hulakov/NosClock/esphome/components/nosclock/nos_controller.h

#pragma once
#include "esphome/core/component.h"
#include "esphome/components/i2c/i2c.h"
#include "esphome/components/time/real_time_clock.h"
#include "esphome/components/output/float_output.h"
#include "esphome/components/light/light_state.h"

#include "nos_effect.h"
#include "effect_solid.h"
#include "effect_digit_sync.h"
#include "effect_scanner.h"
#include "effect_scanner_dual.h"
#include "effect_scanner_split.h"
#include "aw9523.h"
#include "nos_tubes.h"

namespace nosclock {

// Calibrated hardware output limits (1% -> min, 100% -> max)
static constexpr float BACKLIGHT_MIN_RAW = 10.0f;
static constexpr float BACKLIGHT_MAX_RAW = 255.0f;

static constexpr float DOTS_R_MIN_RAW = 1.0f;
static constexpr float DOTS_R_MAX_RAW = 6.0f;

static constexpr float DOTS_G_MIN_RAW = 1.0f;
static constexpr float DOTS_G_MAX_RAW = 4.0f;

static constexpr float DOTS_B_MIN_RAW = 1.0f;
static constexpr float DOTS_B_MAX_RAW = 7.0f;

class NosController : public esphome::PollingComponent {
 public:
   NosController() : esphome::PollingComponent(20) {}

   void setup() override;
   void update() override;
   void dump_config() override;

   void set_i2c_bus(esphome::i2c::I2CBus *bus) { m_i2c_bus = bus; }
   void set_time(esphome::time::RealTimeClock *time) { m_time = time; }
   void set_tubes_light(esphome::light::LightState *light) { m_tubes_light = light; }
   void set_backlight_strip(esphome::light::LightState *strip) { m_backlight_strip = strip; }
   void set_tubes_en(esphome::output::FloatOutput *out) { m_tubes_en = out; }

   void set_clock_enabled(bool enabled) { m_clock_enabled = enabled; }
   bool is_clock_enabled() const { return m_clock_enabled; }
   void toggle_clock() { m_clock_enabled = !m_clock_enabled; }

 private:
   INosEffect &resolve_effect(const std::string &effect_name);
   void update_backlight(esphome::light::AddressableLight *addressable, esphome::light::LightColorValues color_values, esphome::ESPTime time_now, INosEffect &active_effect);
   void update_dots(esphome::light::LightColorValues dots_color_values, esphome::ESPTime time_now, INosEffect &active_effect);

   esphome::i2c::I2CBus *m_i2c_bus = nullptr;
   esphome::time::RealTimeClock *m_time = nullptr;
   esphome::light::LightState *m_tubes_light = nullptr;
   esphome::light::LightState *m_backlight_strip = nullptr;
   esphome::output::FloatOutput *m_tubes_en = nullptr;

   NosTubes m_nos_tubes;
   Aw9523 m_aw9523;
   SolidEffect m_solid_effect{true, false};
   SolidEffect m_static_effect{false, false};
   DigitSyncEffect m_digit_sync_effect;
   ScannerEffect m_scanner_effect;
   ScannerDualEffect m_scanner_dual_effect;
   ScannerSplitEffect m_scanner_split_effect;
   SolidEffect m_cycle_effect{true, true};

   bool m_clock_enabled{true};
};

} // namespace nosclock
