hulakov/NosClock/esphome/components/nosclock/effect_digit_sync.h

#pragma once
#include <array>
#include "nos_effect.h"

namespace nosclock {

class DigitSyncEffect : public INosEffect {
 public:
  std::array<ColorFloat, NUM_LEDS> apply_backlight(esphome::ESPTime time_now, ColorFloat target_color) override;
  std::array<ColorFloat, NUM_DOTS> apply_dots(esphome::ESPTime time_now, ColorFloat target_color) override;
};

} // namespace nosclock
