hulakov/NosClock/esphome/components/nosclock/effect_solid.h

#pragma once
#include <array>
#include "nos_effect.h"

namespace nosclock {

class SolidEffect : public INosEffect {
 public:
  SolidEffect(bool dots_blinks, bool backlight_blinks = false)
      : m_dots_blinks(dots_blinks), m_backlight_blinks(backlight_blinks) {}
  std::array<ColorFloat, NUM_LEDS> apply_backlight(esphome::ESPTime time_now, ColorFloat target_color) override;
  std::array<ColorFloat, NUM_DOTS> apply_dots(esphome::ESPTime time_now, ColorFloat target_color) override;

 private:
  bool m_dots_blinks;
  bool m_backlight_blinks;
};

} // namespace nosclock
